AaronVelez/LI-6800_Lamp/Hardware/COB-LED driver Schematics_v1.1.sch

## EAGLE design Hardware/COB-LED driver Schematics_v1.1.sch (2024-03-08)

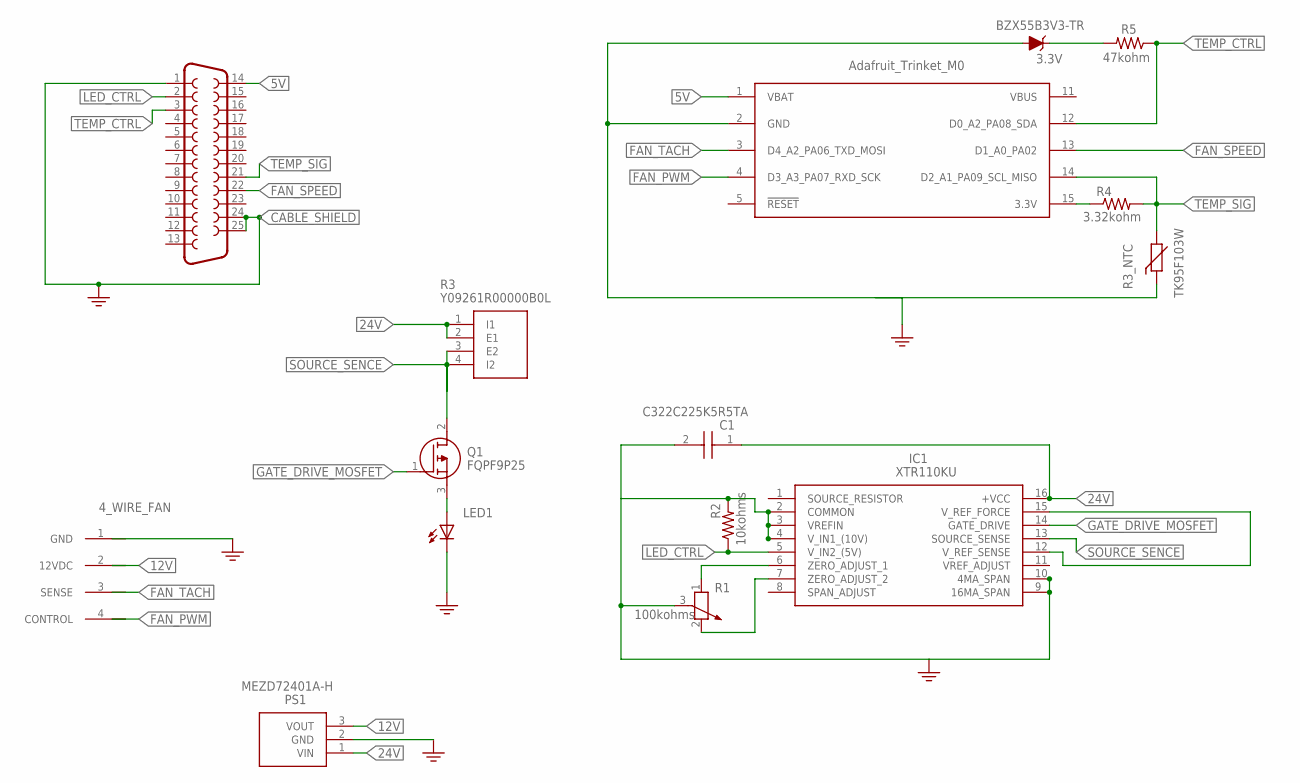
[picture p9: schematic COB-LED driver Schematics_v1.1.sch]

Parts:
C1: C322C225K5R5TA
D1: 3.3V; SOD-323
IC1: XTR110KU; SOIC127P1030X265-16N
LED1: LED; SMARTLED-TTW
PS1: MEZD72401A-H; MEZD72401AH
Q1: FQPF9P25; TO254P490X1016X1970-3P
R1: 100kohms; PT-10
R2: 10kohms; 0309V
R3: Y09261R00000B0L; TO254P401X1016X2196-4P
R3_NTC: THERMISTOR_R-2,5; RS-2,5
R4: 3.32kohm; 0309V
R5: 47kohm; 0309V
U$1: LAMP_IRGA_V1LAMP_IRGA_V1_3D; SOIC127P1032X265-20N
U$2: 4-WIRE-PIN-FAN4-WIRE-PIN-FAN; HDRV4W64P254_1X4_1016X508X838B
X1: F25VP

Connections:
3.3V: LED1.C@1 (C), PS1.2 (GND)
4_WIRE_FAN: U$2.1 (GND)
5V: U$1.1 (VBAT), X1.14
12V: PS1.3 (VOUT), U$2.2 (12VDC)
24V: C1.1, IC1.16 (+VCC), PS1.1 (VIN), R3.1 (I1), R3.2 (E1)
100KOHMS: C1.2, IC1.2 (COMMON), IC1.3 (VREFIN), IC1.4 (V_IN1_(10V)), IC1.9 (16MA_SPAN), IC1.10 (4MA_SPAN), R1.3, R2.2
BZX55B3V3-TR: D1.A, U$1.2 (GND)
CABLE_SHIELD: X1.1, X1.24, X1.25
FAN_PWM: U$1.4 (D3_A3_PA07_RXD_SCK), U$2.4 (CONTROL)
FAN_SPEED: X1.22
FAN_TACH: U$2.3 (SENSE)
GATE_DRIVE_MOSFET: IC1.14 (GATE_DRIVE), Q1.1 (G)
LED_CTRL: IC1.5 (V_IN2_(5V)), R2.1, X1.2
unnamed: IC1.12 (V_REF_SENSE), IC1.15 (V_REF_FORCE)
unnamed: LED1.A@1 (A), Q1.3 (S)
unnamed: IC1.6 (ZERO_ADJUST_1), R1.1
unnamed: R4.1, U$1.15 (3.3V)
unnamed: IC1.7 (ZERO_ADJUST_2), R1.2
unnamed: D1.C, R5.2
SOURCE_SENCE: IC1.13 (SOURCE_SENSE), Q1.2 (D), R3.3 (E2), R3.4 (I2)
TEMP_CTRL: R5.1, U$1.12 (D0_A2_PA08_SDA), X1.3
TEMP_SIG: R3_NTC.2, R4.2, U$1.14 (D2_A1_PA09_SCL_MISO), X1.21
TK95F103W: R3_NTC.1
